Berattaha/quadcopter_flight_controller/images/Image3.jpeg

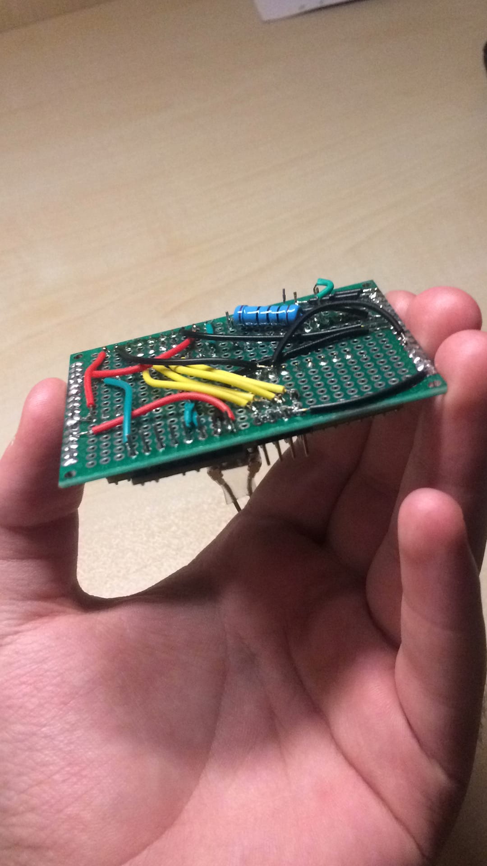
images/Image3.jpeg
