Berattaha/quadcopter_flight_controller/src/drone/a_types.ino

struct ReceiverRawValues {
  bool NewDataAvailable;
  bool TransmitterCommunicationFailure;
  //int ChannelValues[4];
};

struct ReceiverCommands{
  bool Armed;
  bool Error;
  //bool LostFrame;
  double RollAngle;
  double PitchAngle;
  int Throttle;
  double YawAngleChange;
};

struct Orientation {
  double YawAngle;
  double PitchAngle;
  double RollAngle;
};

struct IMU_Values {
  bool Error;
  bool NewDataAvailable;
  double DeltaTimeInSeconds;
  struct Orientation CurrentOrientation;
  struct Orientation PreviousOrientation;
};

struct MotorPowers {
  int frontLeftMotorPower;
  int frontRightMotorPower;
  int rearLeftMotorPower;
  int rearRightMotorPower;
};
